shuy98/24354TP/img/IMG_9759.jpg

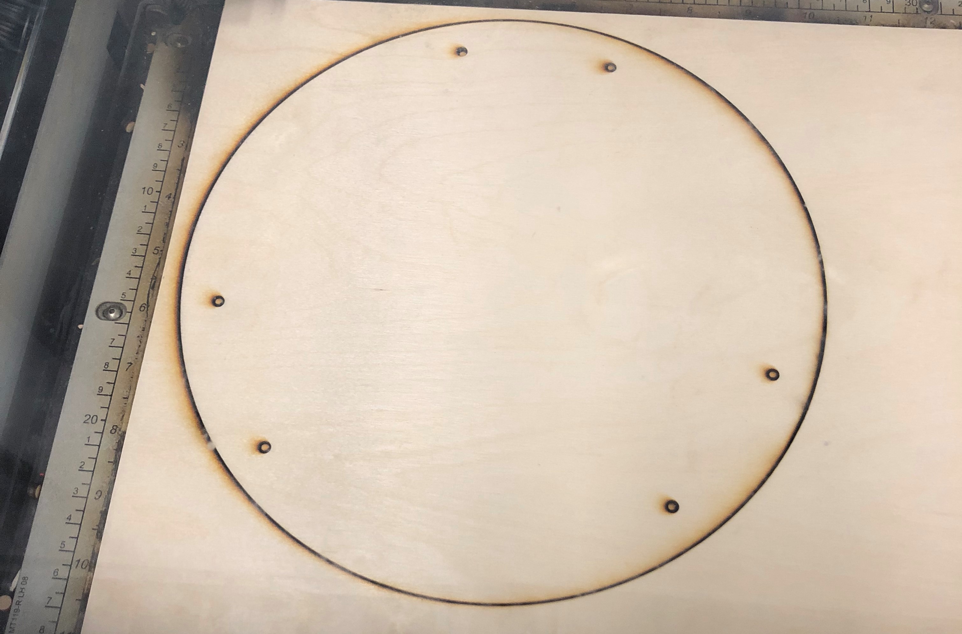
img/IMG_9759.jpg
