shuy98/24354TP/img/微信图片_20181130145501.jpg

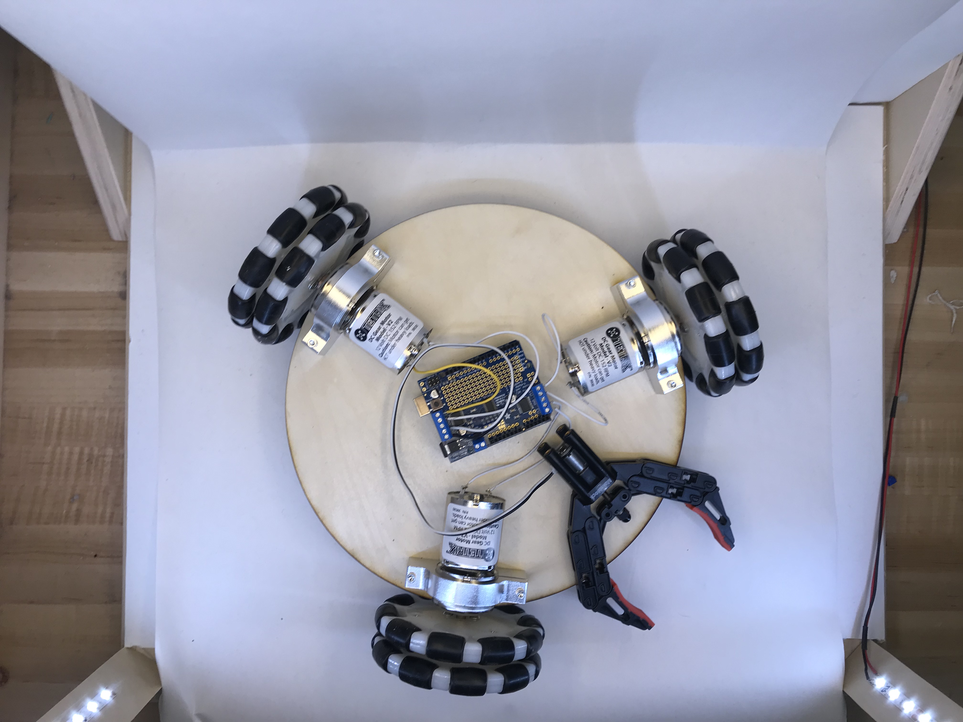
img/微信图片_20181130145501.jpg
