shuy98/24354TP/presentation/img/Angle_3.JPG

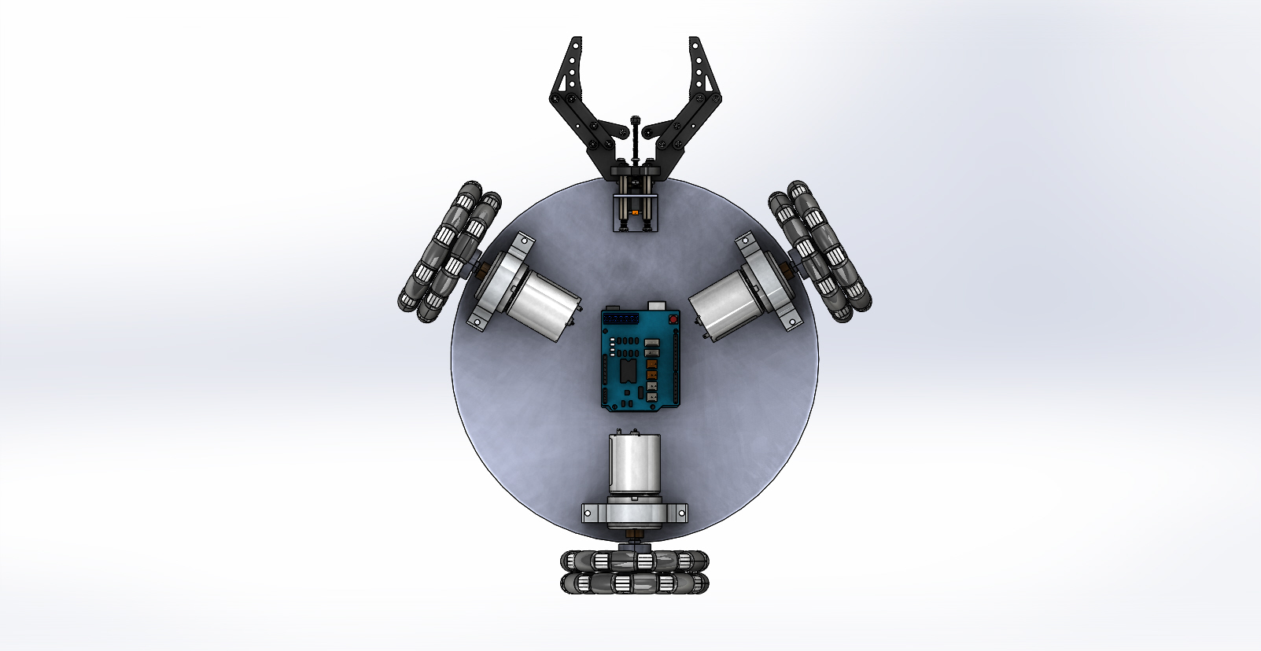
presentation/img/Angle_3.JPG
