shuy98/24354TP/presentation/img/Angle_4.JPG

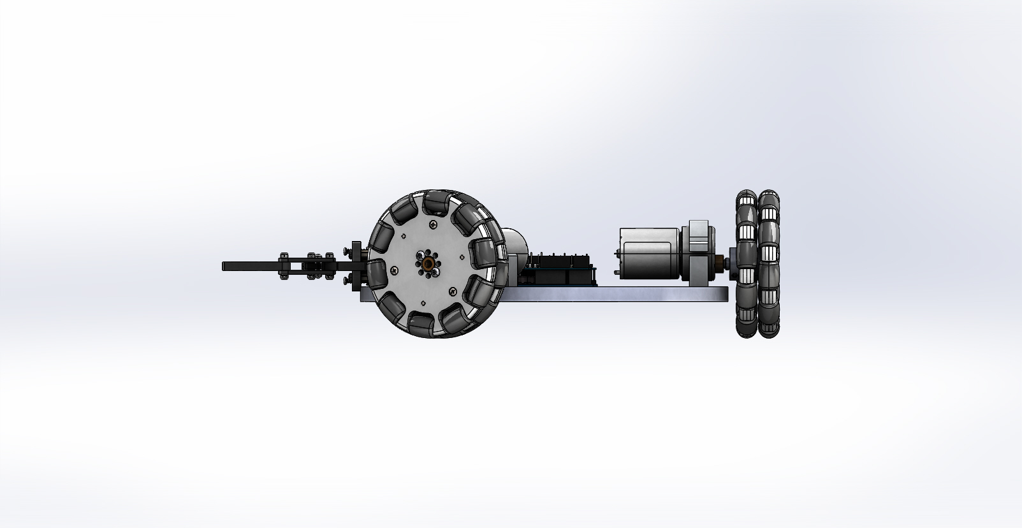
presentation/img/Angle_4.JPG
