shuy98/24354TP/presentation/img/Capture.JPG

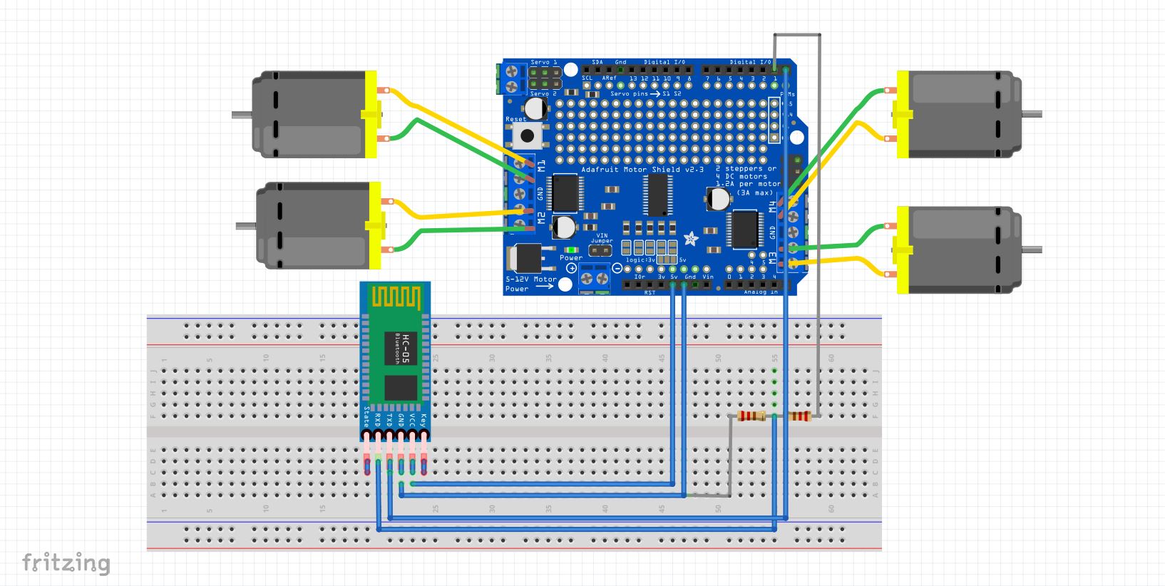
presentation/img/Capture.JPG
