shuy98/24354TP/presentation/img/code2flow_b9eb1.png

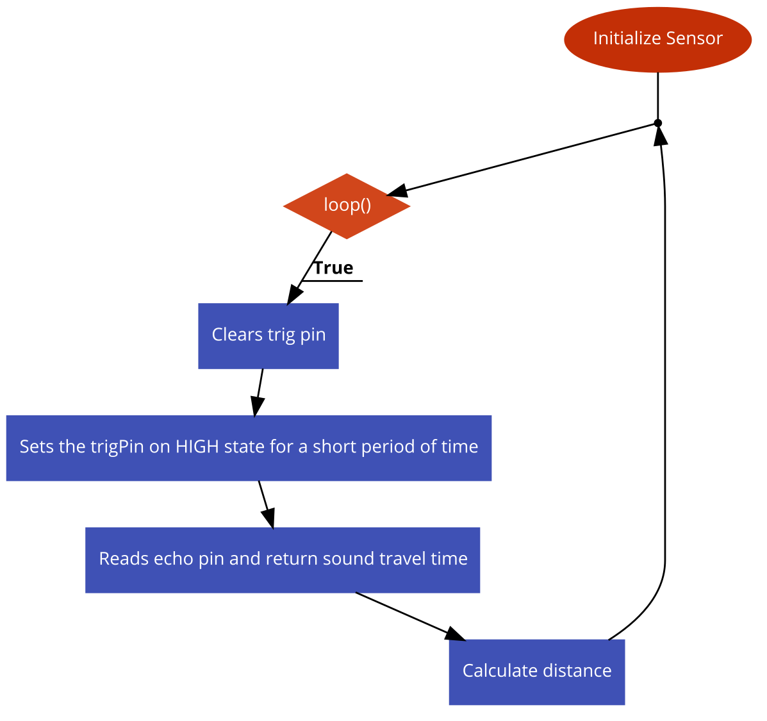
presentation/img/code2flow_b9eb1.png
