shuy98/24354TP/presentation/img/code2flow_c28d7.png

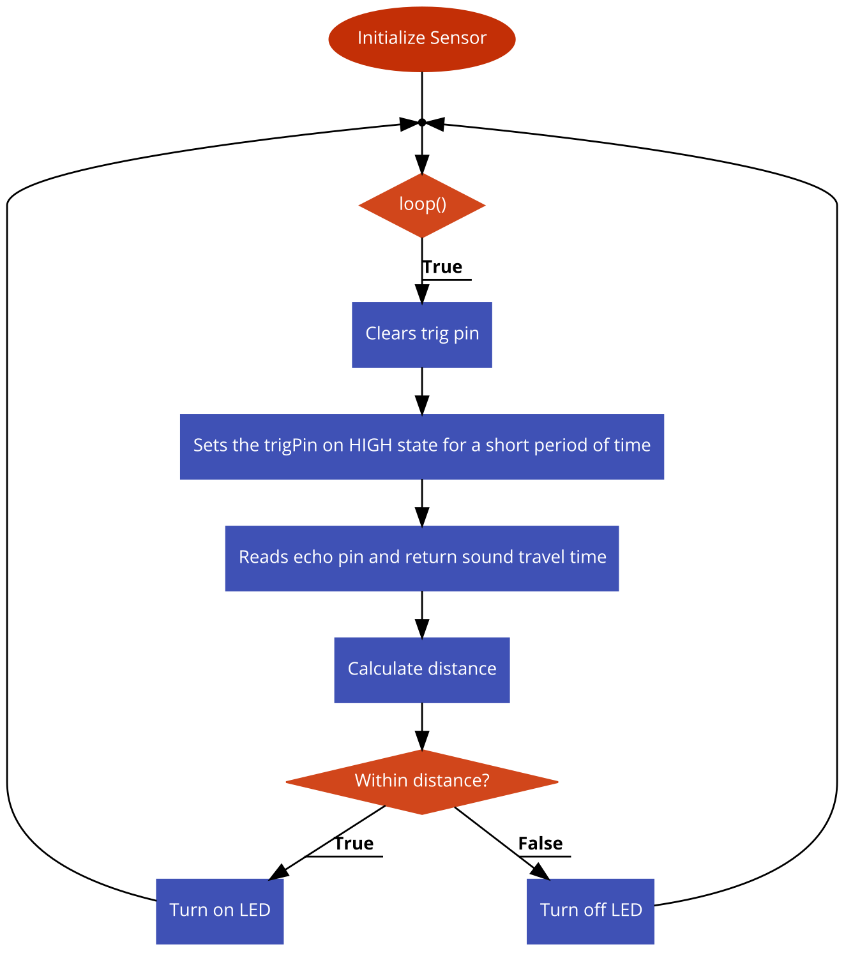
presentation/img/code2flow_c28d7.png
